thomaseleff/Ospro/ospro/platform/raspberry_pi.py

""" Raspberry-Pi general-purpose input / output interface """

from ospro import exceptions

# Import raspberry-pi general-purpose input / output interface.
try:
    import RPi.GPIO as GPIO

    # Define the board mode
    if not GPIO.getmode():
        GPIO.setmode(GPIO.BCM)
    elif GPIO.getmode() == 10:
        raise exceptions.InvalidModeError(
            'Invalid interface mode {BOARD}.'
        )
    else:
        pass

except ImportError:
    raise exceptions.InvalidPlatformError(
        ' '.join([
            'Invalid platform.',
            'The {raspberry-pi} platform requires the {rpi} hardware',
            'libraries. Install them with `uv sync --extra rpi`.'
        ])
    )


def Interface():
    """ Represents the Raspberry-Pi general-purpose input / output interface.
    """
    return GPIO
